ayuusweetfish/Malletwand/testdrive/cli/ekf_test.c

#include <stdio.h>
#include <time.h>
#include "ekf.h"
#include "ekf_unopt.h"

const float z[][2] = {
{-0.30363700,0.15020664}, {-0.30631390,0.23414357}, {-0.38538748,0.23246633}, {-0.60523939,0.19448967}, {-0.57978481,0.28296620}, {-0.50962692,0.32203233}, {-0.24314955,0.30328578}, {-0.12464703,0.28733385}, {-0.10175940,0.22583233}, {-0.11645509,0.18484612}, {-0.13042359,0.06592835}, {-0.11888476,0.02425108}, {0.09917477,-0.29184744}, {0.19101466,-0.40515721}, {0.14989164,-0.39028764}, {0.14948493,-0.47371718}, {0.38135502,-0.71502864}, {0.38196054,-0.72479922}, {0.17213143,-0.48575068}, {0.32378760,-0.51375544}, {0.35252827,-0.48075166}, {0.19650212,-0.30821061}, {0.11248349,-0.20600942}, {0.02866993,-0.04447396}, {0.01317717,0.05961587}, {-0.03961469,0.10225092}, {-0.24324547,0.14320348}, {-0.39089668,0.16226968}, {-0.49451840,0.26791102}, {-0.39591488,0.42068666}, {-0.57746482,0.45009291}, {-0.56653476,0.48279351}, {-0.43490672,0.56886917}, {-0.29006797,0.61037761}, {-0.24318063,0.57972658}, {-0.29184777,0.48923224}, {-0.13847764,0.38742971}, {0.04041527,0.26320687}, {0.04127733,0.10215056}, {-0.06463777,-0.13701807}, {-0.06478415,-0.24504828}, {0.07744804,-0.43994418}, {0.18473396,-0.49606803}, {0.23622359,-0.51487195}, {0.20895399,-0.53060424}, {0.04783802,-0.60734791}, {0.07254527,-0.65975434}, {0.33131307,-0.63892496}, {0.23582080,-0.56343132}, {0.18280277,-0.52789599}, {0.17084940,-0.39010203}, {0.22951111,-0.34484938}, {-0.03699742,-0.05722602}, {-0.18140292,0.07026660}, {-0.23760802,0.23089249}, {-0.26650369,0.27747458}, {-0.35925886,0.25081539}, {-0.54818219,0.328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
};

int main()
{
  float x[5] = {40, 1, fmod(1e4, M_PI * 2), 1, fmod(1e4, M_PI * 2)};
  float P[5][5] = {
    {30, 0, 0, 0, 0},
    {0, 1, 0, 0, 0},
    {0, 0, 4, 0, 0},
    {0, 0, 0, 1, 0},
    {0, 0, 0, 0, 4},
  };

  int n = sizeof z / sizeof z[0];
/*
  for (int i = 0; i < n * 100; i++) {
    ekf_step(x, P, z[i % n]);
    printf("%.5f\n", x[2]);
  }
*/

  for (int i = 0; i < 10; i++) {
    clock_t start = clock();
    float x[5] = {40, 1, 0, 1, 0};
    float P[5][5] = {{30, 0, 0, 0, 0}, {0, 1, 0, 0, 0}, {0, 0, 4, 0, 0}, {0, 0, 0, 1, 0}, {0, 0, 0, 0, 4}};
    for (int j = 0; j < n * 100; j++) {
      ekf_step(x, P, z[j % n]);
      if (i == 1 && (j + 1) % (n * 10) == 0) printf("Opt result (%d): %.8f\n", j, x[2]);
    }
    printf("Time: %.6f\n", (float)(clock() - start) / CLOCKS_PER_SEC);
  }

  for (int i = 0; i < 10; i++) {
    clock_t start = clock();
    float x[5] = {40, 1, 0, 1, 0};
    float P[5][5] = {{30, 0, 0, 0, 0}, {0, 1, 0, 0, 0}, {0, 0, 4, 0, 0}, {0, 0, 0, 1, 0}, {0, 0, 0, 0, 4}};
    for (int j = 0; j < n * 100; j++) {
      ekf_step_unopt(x, P, z[j % n]);
      if (i == 1 && (j + 1) % (n * 10) == 0) printf("Unopt result (%d): %.8f\n", j, x[2]);
    }
    printf("Time: %.6f\n", (float)(clock() - start) / CLOCKS_PER_SEC);
  }

  return 0;
}
